psiquo/the-annoying-alarm/ArduinoMega/CarHandler/Serial.ino

void setup_serial() {
  Serial1.begin(9600);
}
void handle_serial() {
  if(Serial1.available()){
    String msg = Serial1.readStringUntil("\n");
    msg.trim();
    Serial.print("Received message: " + msg + "\n");
    if(msg.equals("en")){
      enabled = true;
    } else if(msg.equals("dis")){
      enabled = false;
    }
  } 
}
